whowechina/nos_pico/ref/1707077977.8098.jpg

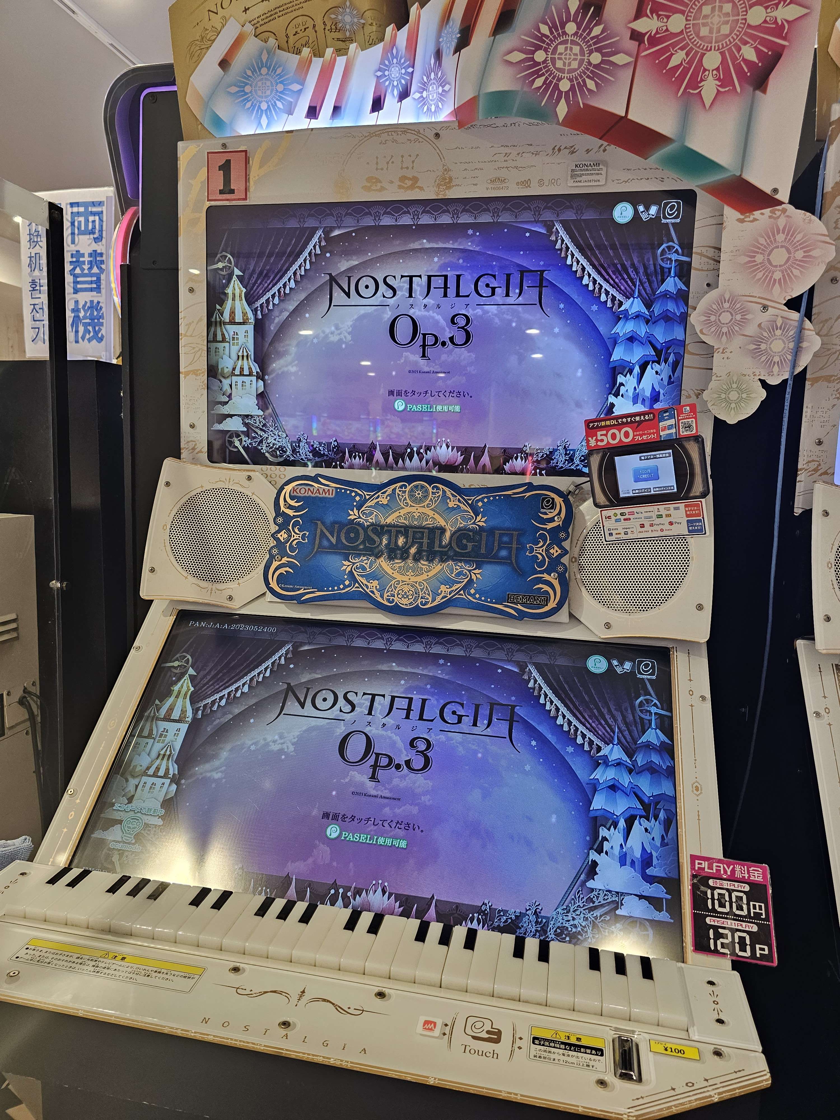
ref/1707077977.8098.jpg
