whowechina/nos_pico/Production/3DPrint/Nos Pico - Support Left.stl

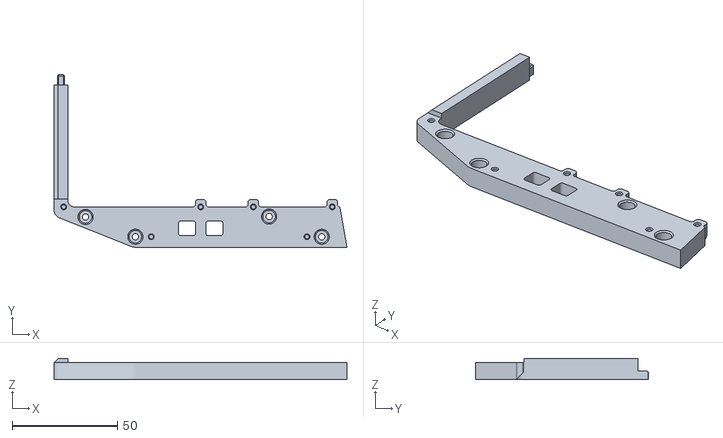
[picture p39: CAD file, 2025-03-28]
Production/3DPrint/Nos Pico - Support Left.stl
139.2 x 82.0 x 10.0
