whowechina/nos_pico/PCB/pico/3dmodels/EVQ-P1D05M.stp

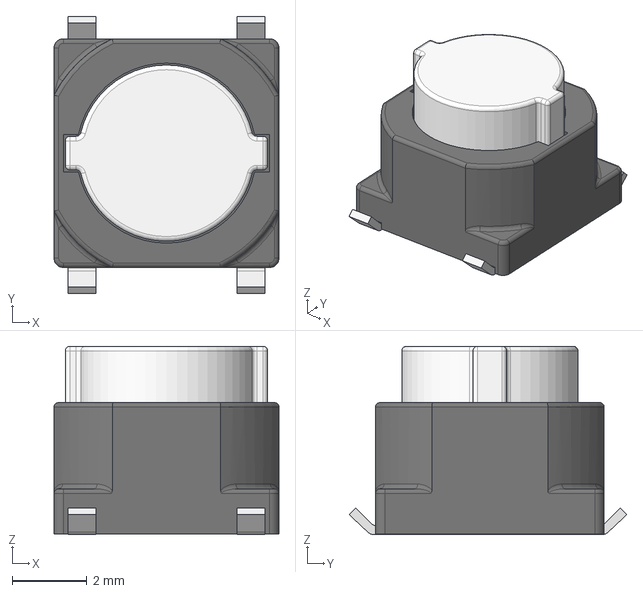
[picture p40: CAD file, 2025-02-28]
PCB/pico/3dmodels/EVQ-P1D05M.stp
6.00 x 7.40 x 5.03 mm
