whowechina/nos_pico/Production/3DPrint/Nos Pico - Support Center.stl

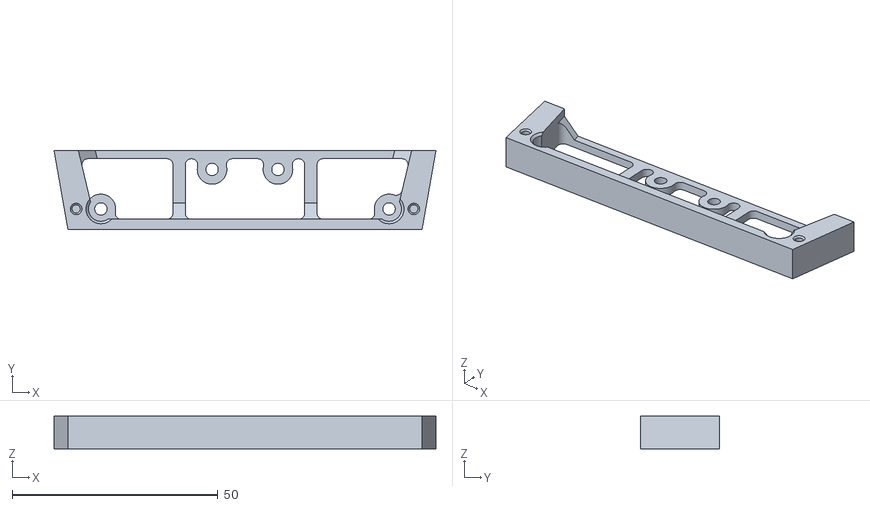
[picture p41: CAD file, 2025-03-28]
Production/3DPrint/Nos Pico - Support Center.stl
92.8 x 19.2 x 8.00
