whowechina/nos_pico/PCB/plus/3dmodels/ADG732BSUZ.step

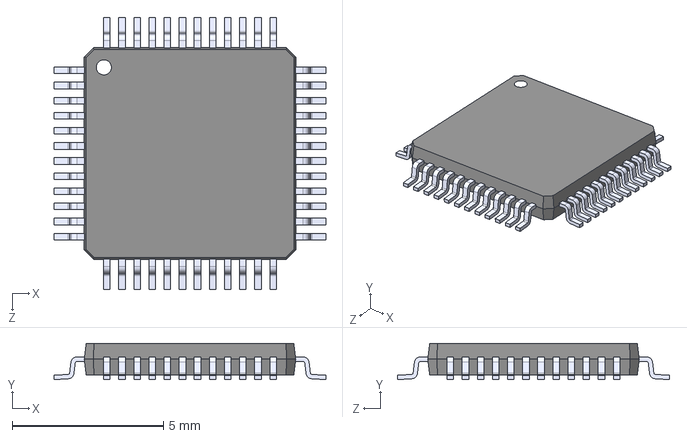
[picture p42: CAD file, 2025-02-28]
PCB/plus/3dmodels/ADG732BSUZ.step
9.00 x 1.20 x 9.00 mm
