whowechina/nos_pico/Production/3DPrint/Nos Pico - Panel Center.3mf

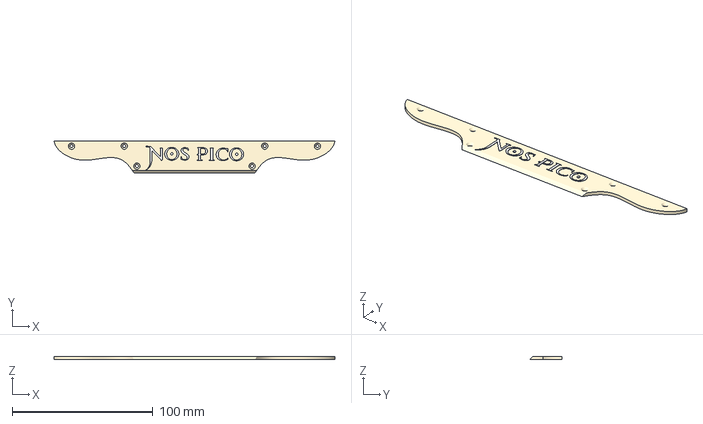
[picture p43: CAD file, 2025-03-28]
Production/3DPrint/Nos Pico - Panel Center.3mf
200.0 x 23.0 x 2.20 mm
