whowechina/nos_pico/PCB/pico/3dmodels/User Library-WS2812-2020.step

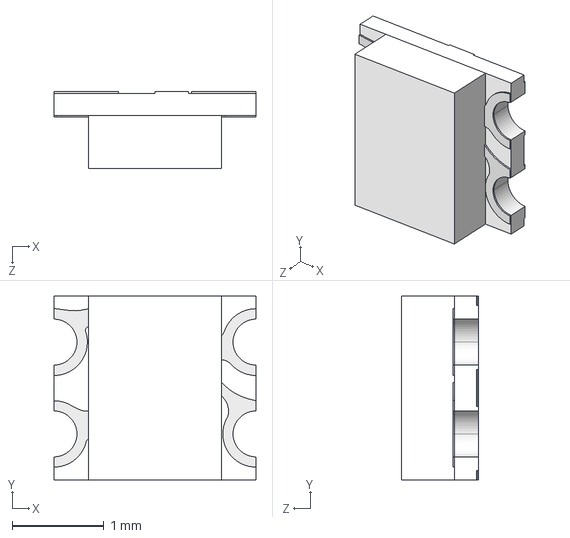
[picture p44: CAD file, 2025-02-28]
PCB/pico/3dmodels/User Library-WS2812-2020.step
2.20 x 2.00 x 0.84 mm
