whowechina/nos_pico/Production/3DPrint/Nos Pico - Key.3mf

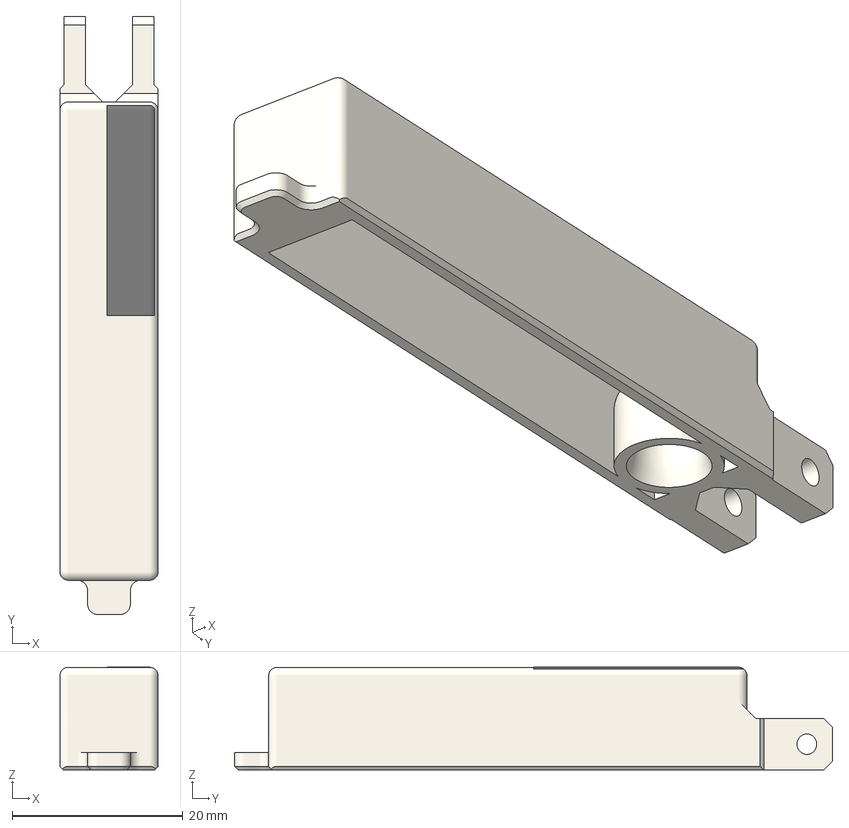
[picture p45: CAD file, 2025-03-28]
Production/3DPrint/Nos Pico - Key.3mf
11.5 x 70.0 x 12.0 mm
WhiteKey
BlackKey
