whowechina/nos_pico/PCB/plus/3dmodels/SKSTAAE010.STEP

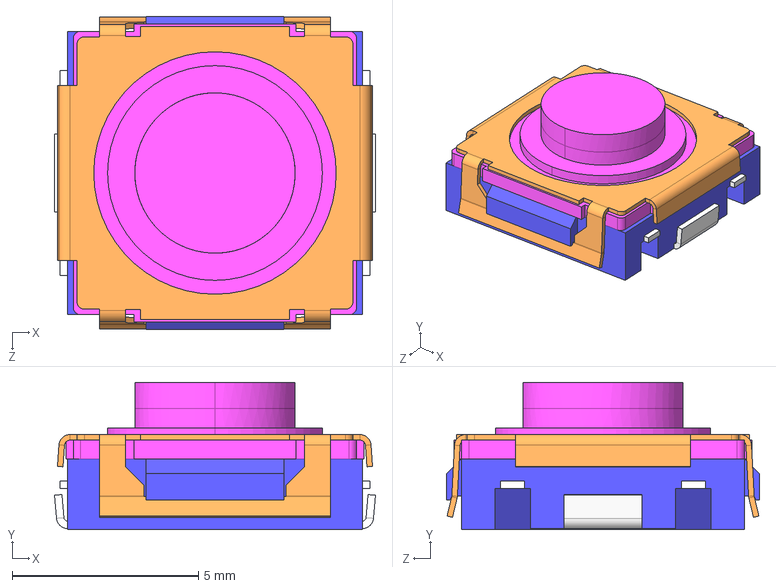
[picture p46: CAD file, 2025-02-28]
PCB/plus/3dmodels/SKSTAAE010.STEP
8.61 x 3.95 x 8.40 mm
