whowechina/nos_pico/Production/3DPrint/Nos Pico - Rear Center.stl

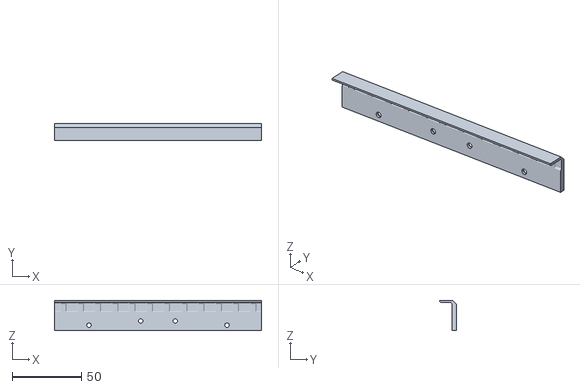
[picture p47: CAD file, 2025-03-28]
Production/3DPrint/Nos Pico - Rear Center.stl
150.0 x 12.0 x 22.0
