whowechina/nos_pico/PCB/pico/3dmodels/SMD WS2812B-3535.step

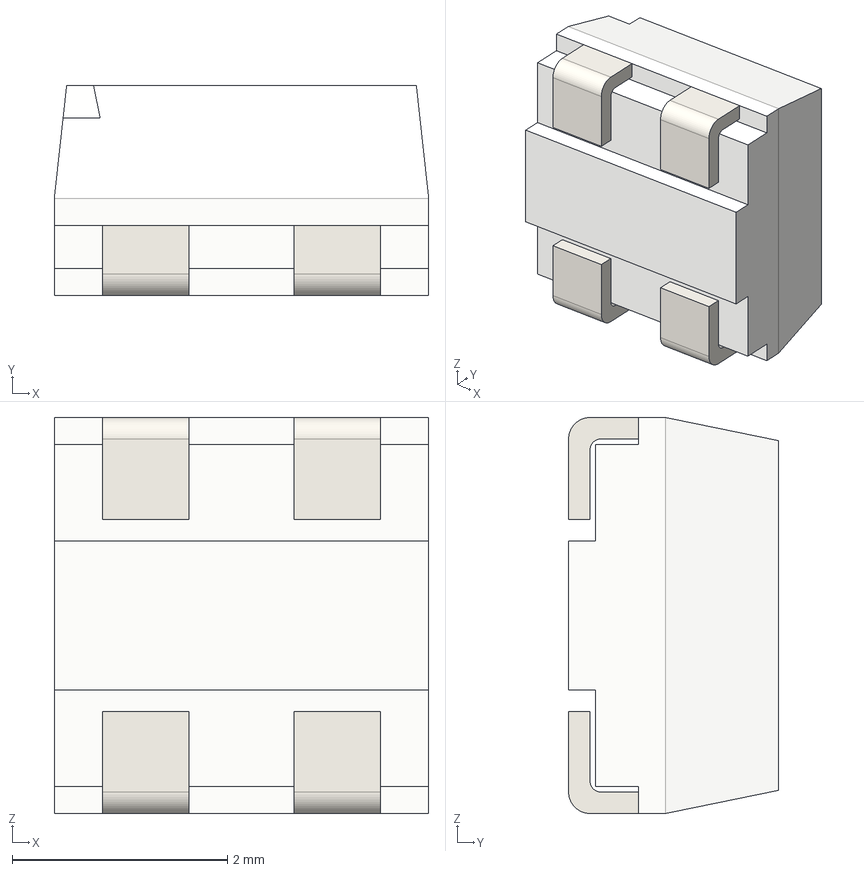
[picture p48: CAD file, 2025-02-28]
PCB/pico/3dmodels/SMD WS2812B-3535.step
3.48 x 1.95 x 3.68 mm
